KubaMiszcz/KwadraLampa/foto/2017-06-14 105718.jpg

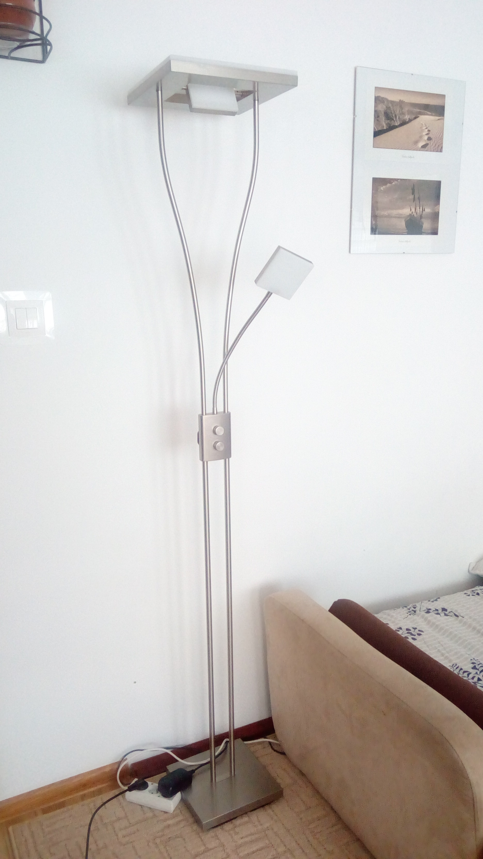
foto/2017-06-14 105718.jpg
