KubaMiszcz/KwadraLampa/foto/2017-06-14 105728.jpg

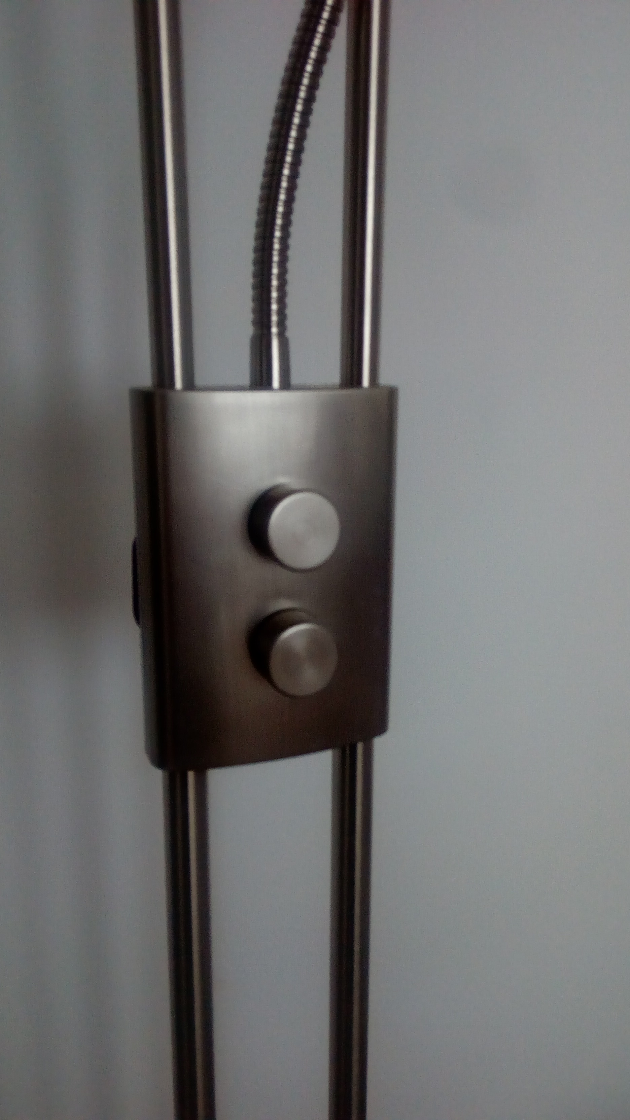
foto/2017-06-14 105728.jpg
