KubaMiszcz/KwadraLampa/foto/2017-06-14 105741.jpg

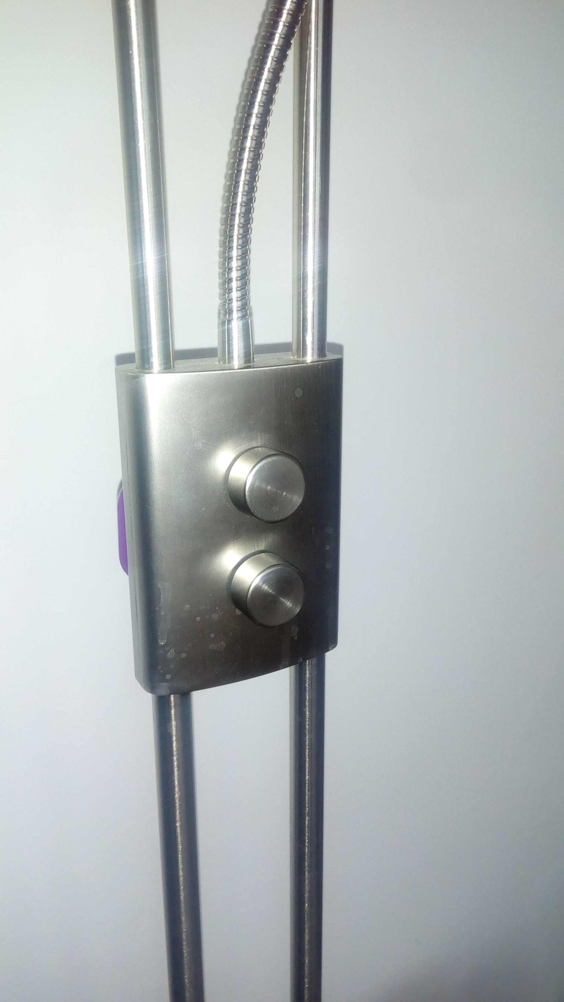
foto/2017-06-14 105741.jpg
