KubaMiszcz/KwadraLampa/foto/2017-06-16 212329.jpg

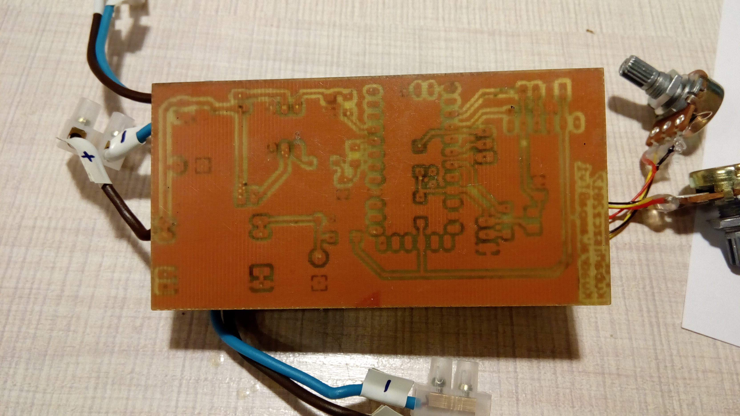
foto/2017-06-16 212329.jpg
