KubaMiszcz/KwadraLampa/foto/2017-06-16 212456.jpg

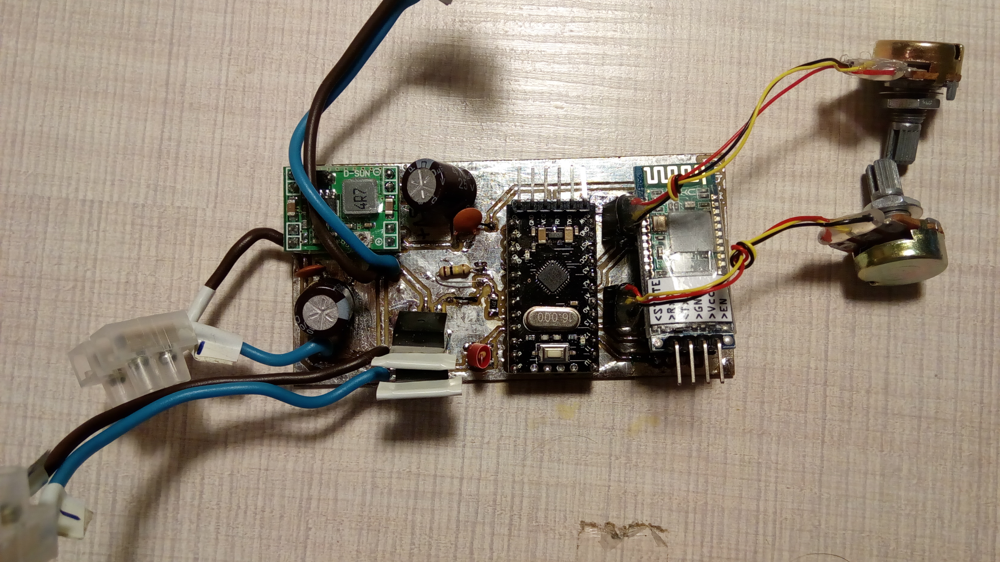
foto/2017-06-16 212456.jpg
