KubaMiszcz/KwadraLampa/foto/2017-06-16 212521.jpg

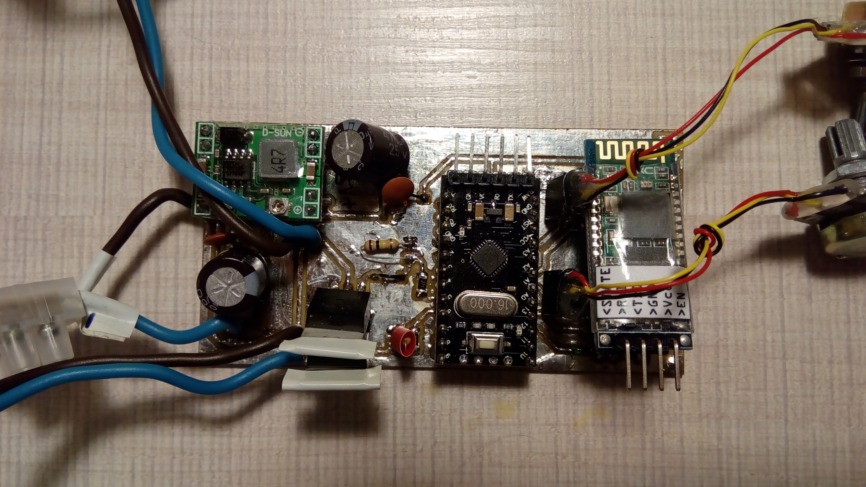
foto/2017-06-16 212521.jpg
