KubaMiszcz/KwadraLampa/foto/foto stara plytka oryginalna/2017-04-05 090402.jpg

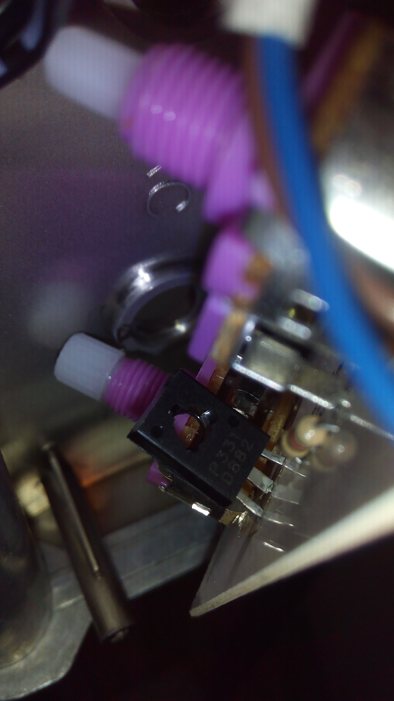
foto/foto stara plytka oryginalna/2017-04-05 090402.jpg
