KubaMiszcz/KwadraLampa/foto/foto stara plytka oryginalna/2017-04-05 090437.jpg

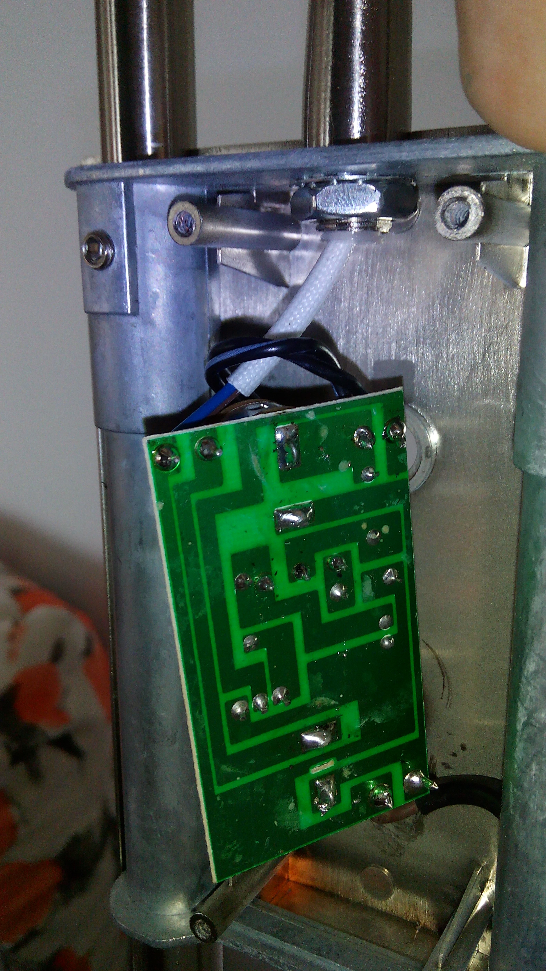
foto/foto stara plytka oryginalna/2017-04-05 090437.jpg
