KubaMiszcz/KwadraLampa/foto/foto stara plytka oryginalna/2017-04-20 123041.jpg

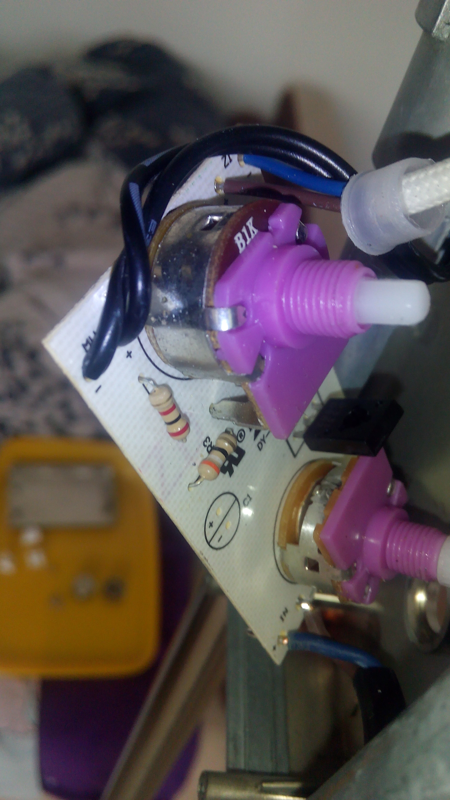
foto/foto stara plytka oryginalna/2017-04-20 123041.jpg
