KubaMiszcz/KwadraLampa/foto/foto stara plytka oryginalna/2017-04-20 140759.jpg

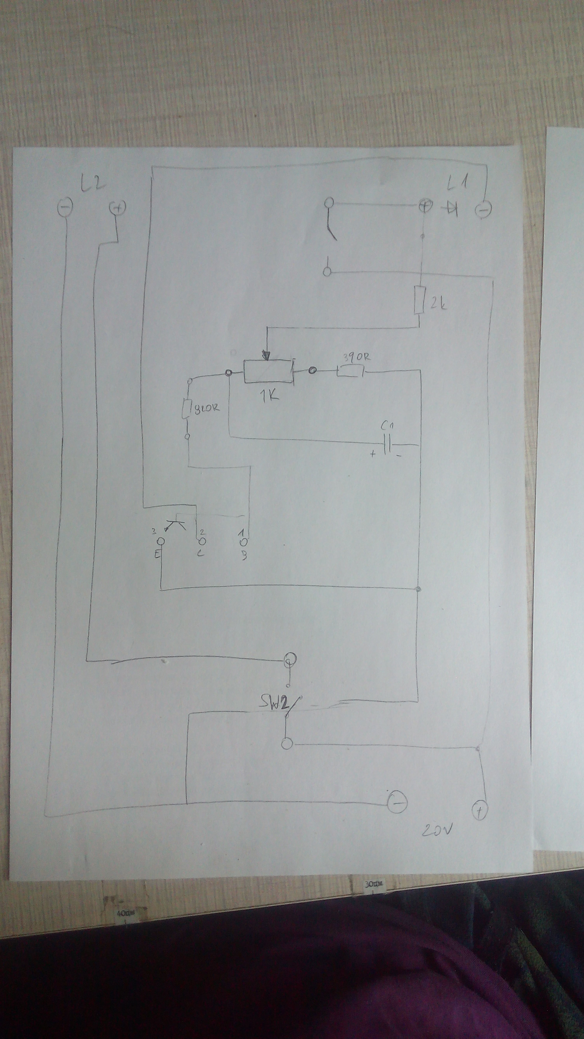
foto/foto stara plytka oryginalna/2017-04-20 140759.jpg
