KubaMiszcz/KwadraLampa/foto/foto stara plytka oryginalna/2017-04-21 072605.jpg

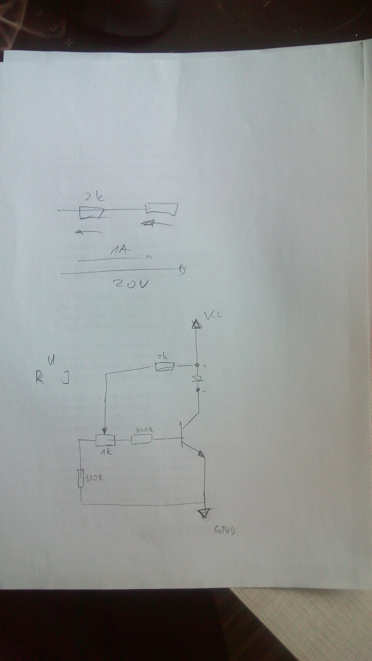
foto/foto stara plytka oryginalna/2017-04-21 072605.jpg
