KubaMiszcz/KwadraLampa/foto/Screenshot_20170625-214846-649.jpg

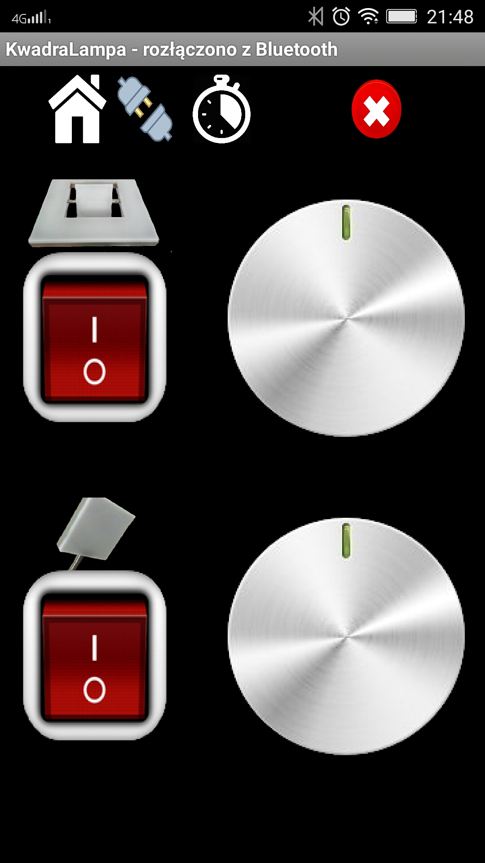
foto/Screenshot_20170625-214846-649.jpg
