KubaMiszcz/KwadraLampa/foto/Screenshot_20170625-214859-454.jpg

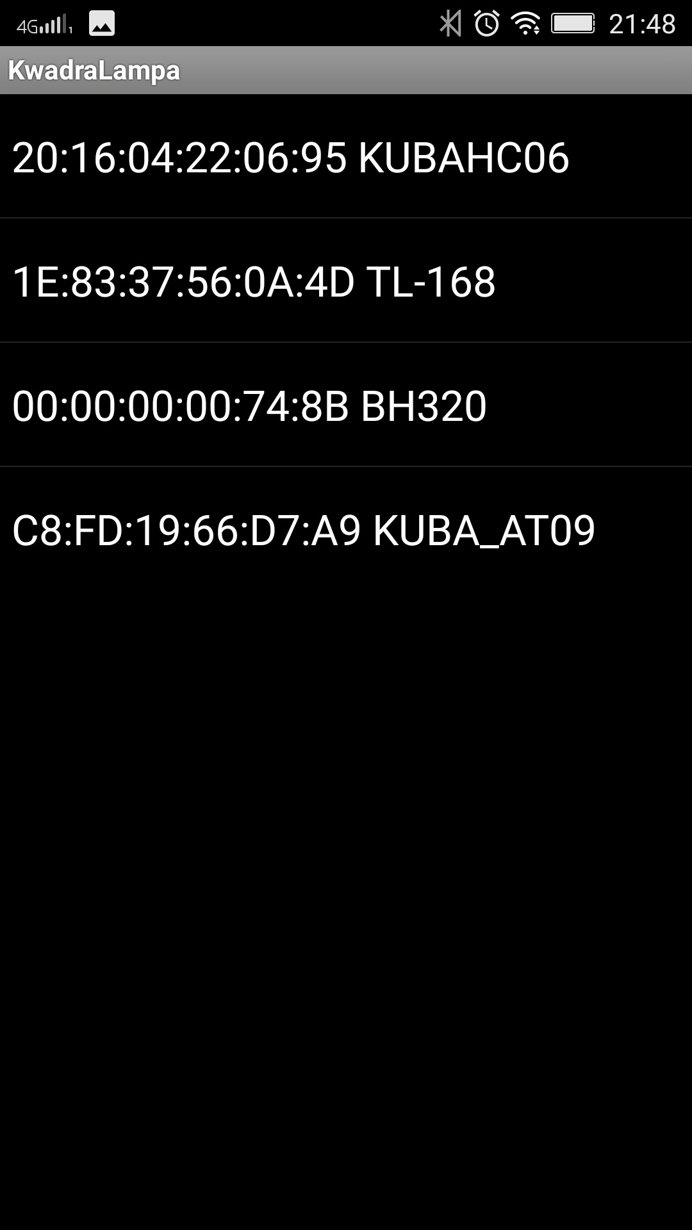
foto/Screenshot_20170625-214859-454.jpg
