KubaMiszcz/KwadraLampa/foto/Screenshot_20170625-214941-489.jpg

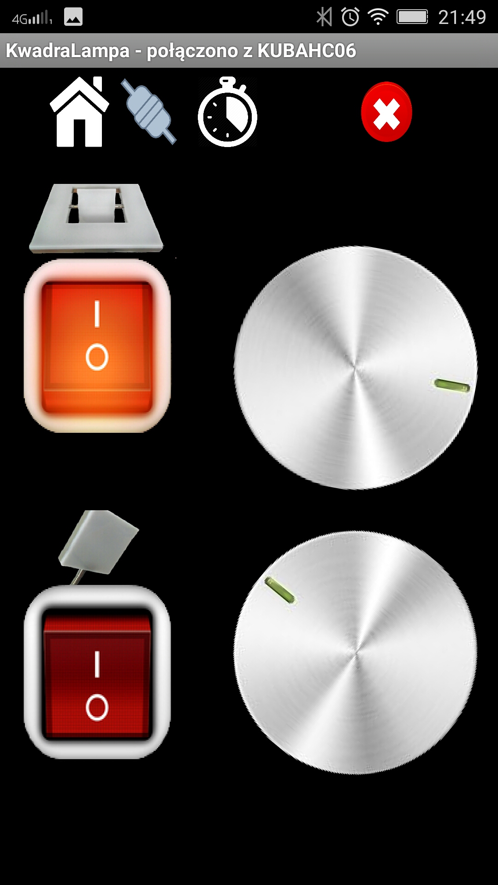
foto/Screenshot_20170625-214941-489.jpg
