KubaMiszcz/KwadraLampa/grafiki/=accepted/configmgtmv2.png

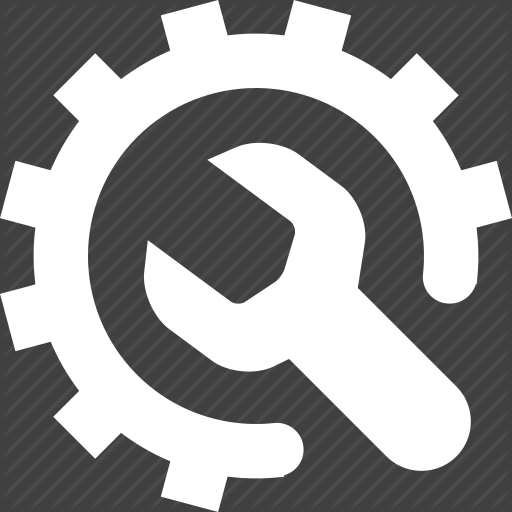
grafiki/=accepted/configmgtmv2.png
