KubaMiszcz/KwadraLampa/grafiki/=accepted/connected.png

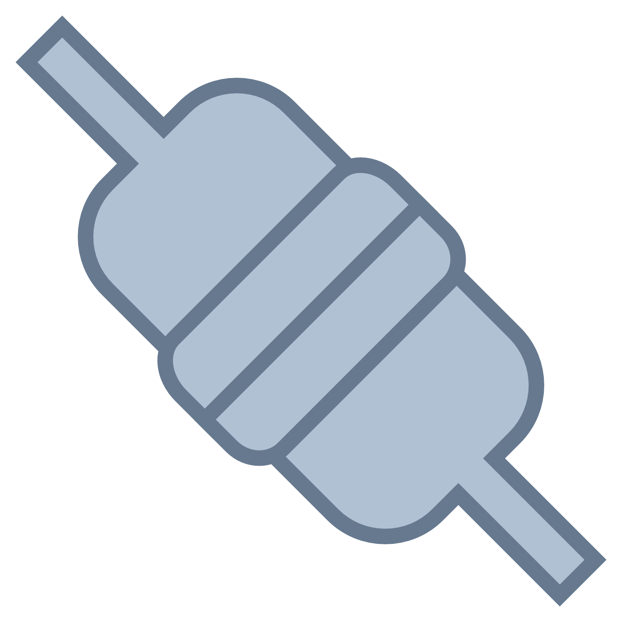
grafiki/=accepted/connected.png
