KubaMiszcz/KwadraLampa/grafiki/=accepted/disconnected.png

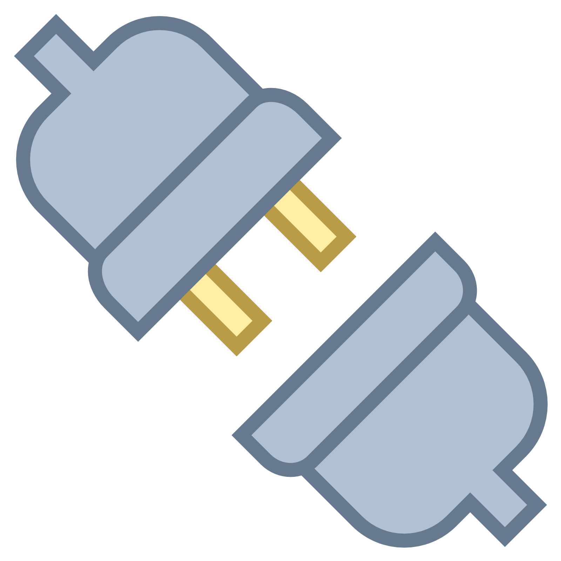
grafiki/=accepted/disconnected.png
