KubaMiszcz/KwadraLampa/grafiki/=accepted/rotaryframe.png

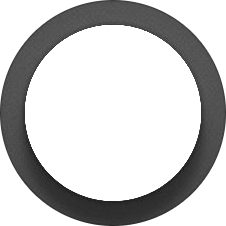
grafiki/=accepted/rotaryframe.png
