KubaMiszcz/KwadraLampa/grafiki/=accepted/rotaryknob.png

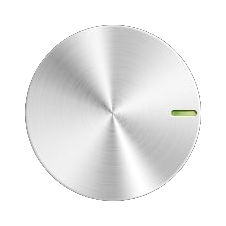
grafiki/=accepted/rotaryknob.png
