KubaMiszcz/KwadraLampa/grafiki/=accepted/rotaryknobv2.png

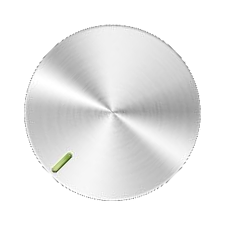
grafiki/=accepted/rotaryknobv2.png
