KubaMiszcz/KwadraLampa/grafiki/=accepted/rotaryknobv3.png

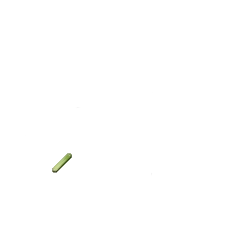
grafiki/=accepted/rotaryknobv3.png
