KubaMiszcz/KwadraLampa/grafiki/=accepted/tglOFF.png

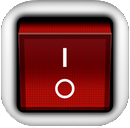
grafiki/=accepted/tglOFF.png
