KubaMiszcz/KwadraLampa/grafiki/=accepted/tglON.png

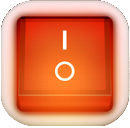
grafiki/=accepted/tglON.png
