KubaMiszcz/KwadraLampa/grafiki/rotary knob/1be09ef4f67cd16aef867e28d9eb9c2ec.jpg

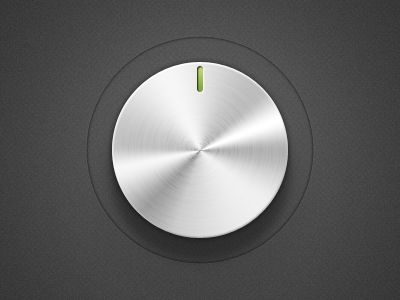
grafiki/rotary knob/1be09ef4f67cd16aef867e28d9eb9c2ec.jpg
