KubaMiszcz/KwadraLampa/grafiki/rotary knob/12.jpg

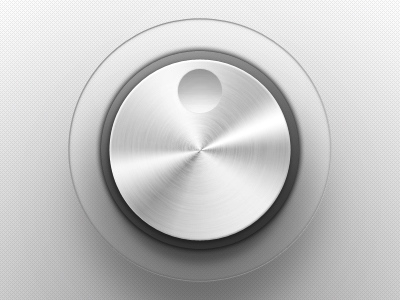
grafiki/rotary knob/12.jpg
