KubaMiszcz/KwadraLampa/grafiki/rotary knob/44b840771f93643ba0205818fd45a70e.jpg

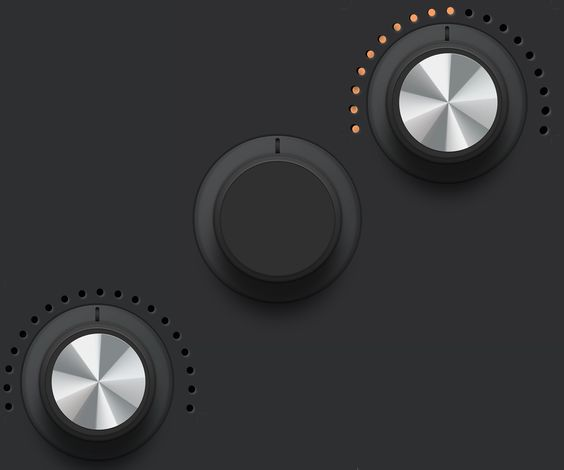
grafiki/rotary knob/44b840771f93643ba0205818fd45a70e.jpg
