KubaMiszcz/KwadraLampa/grafiki/rotary knob/175a313ea760b521a13a66fa4a31e26b.jpg

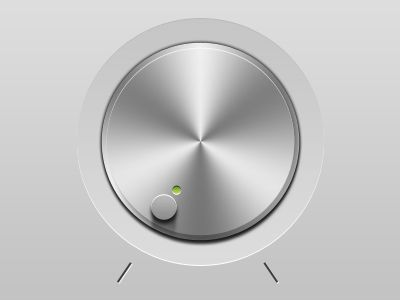
grafiki/rotary knob/175a313ea760b521a13a66fa4a31e26b.jpg
