KubaMiszcz/KwadraLampa/grafiki/rotary knob/0339cee554c793700000158fcb66db1.jpg

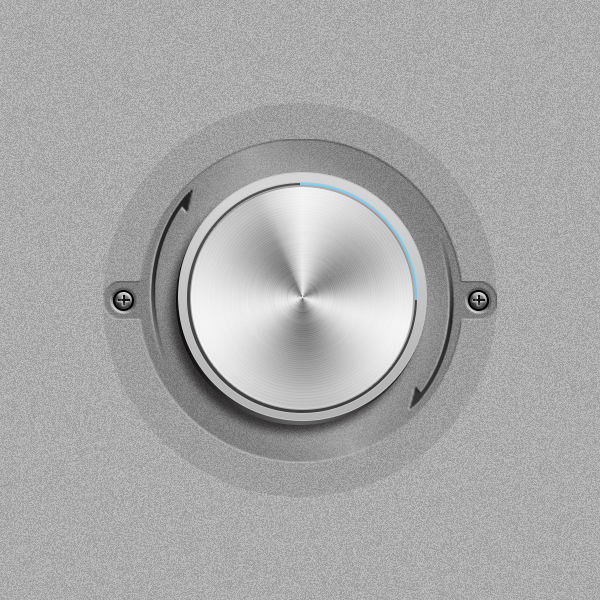
grafiki/rotary knob/0339cee554c793700000158fcb66db1.jpg
