KubaMiszcz/KwadraLampa/grafiki/rotary knob/658cad4266a4e6def83f9c6049b5e742.jpg

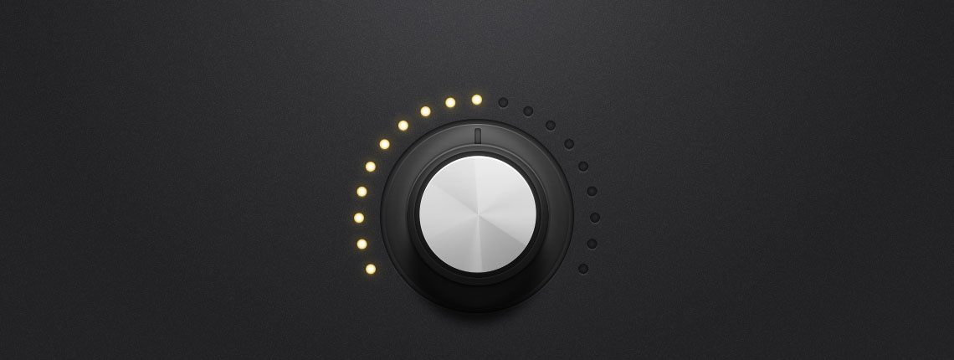
grafiki/rotary knob/658cad4266a4e6def83f9c6049b5e742.jpg
