KubaMiszcz/KwadraLampa/grafiki/rotary knob/201359c53ff9c94d0415b635d4622114.jpg

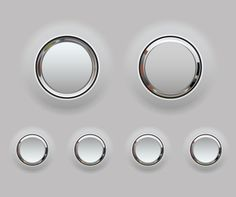
grafiki/rotary knob/201359c53ff9c94d0415b635d4622114.jpg
