KubaMiszcz/KwadraLampa/grafiki/rotary knob/13725800696028.jpg

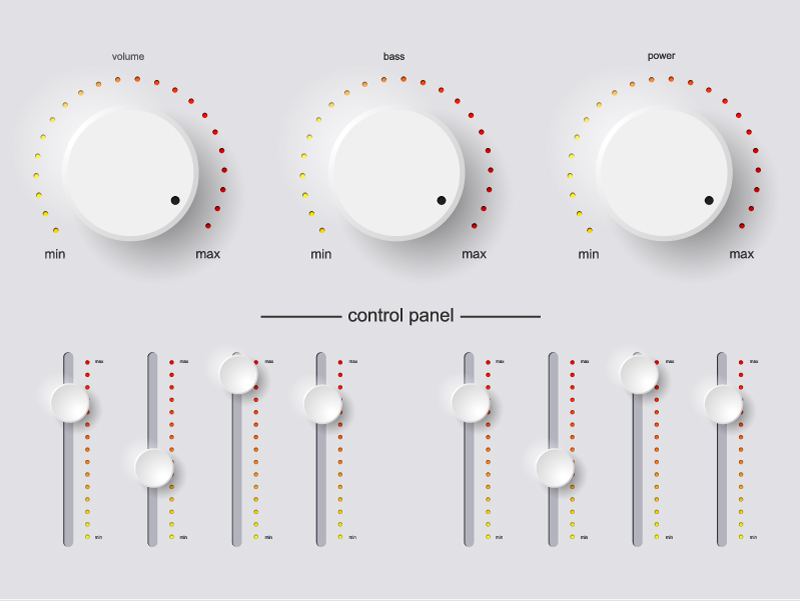
grafiki/rotary knob/13725800696028.jpg
