KubaMiszcz/KwadraLampa/grafiki/rotary knob/cc8fb4c5d4ede3740c84c0babd9590ac-d5dccy2.jpg

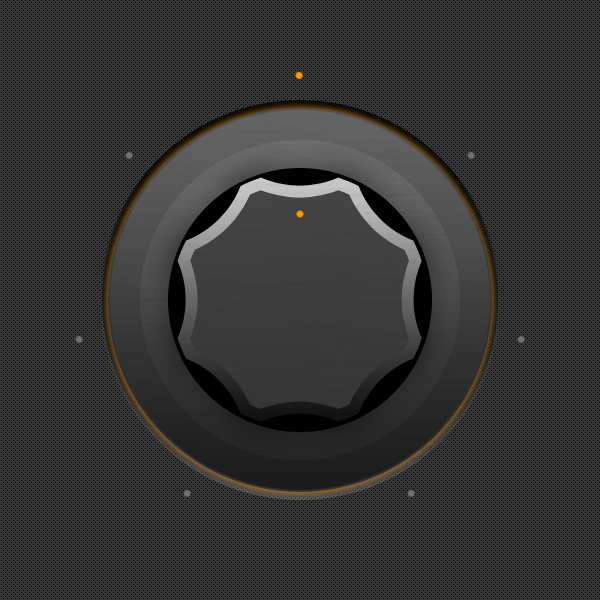
grafiki/rotary knob/cc8fb4c5d4ede3740c84c0babd9590ac-d5dccy2.jpg
