KubaMiszcz/KwadraLampa/grafiki/rotary knob/d845cab26f0945b9a81a3039507318fb.jpg

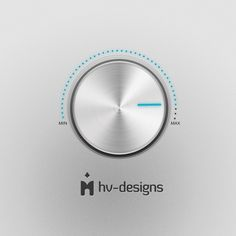
grafiki/rotary knob/d845cab26f0945b9a81a3039507318fb.jpg
