KubaMiszcz/KwadraLampa/grafiki/rotary knob/e2a8a074b16d124590965471c6b21355.jpg

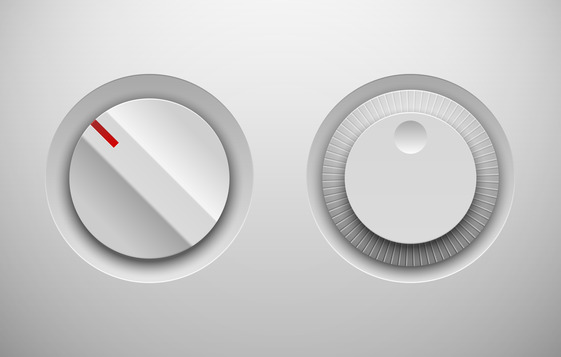
grafiki/rotary knob/e2a8a074b16d124590965471c6b21355.jpg
