KubaMiszcz/KwadraLampa/grafiki/rotary knob/elevator_btn_port.jpg

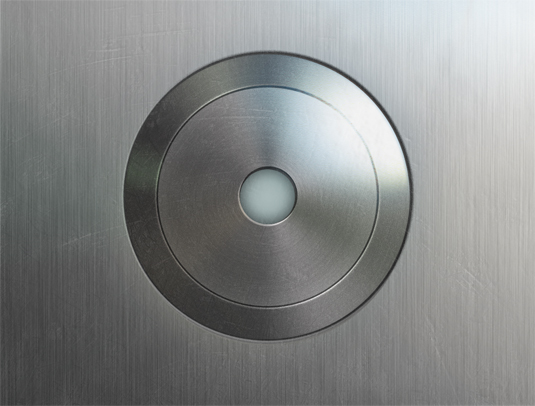
grafiki/rotary knob/elevator_btn_port.jpg
