KubaMiszcz/KwadraLampa/grafiki/rotary knob/High-quality-psd-files-1sept-34.jpg

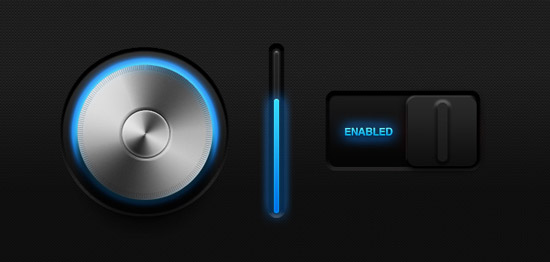
grafiki/rotary knob/High-quality-psd-files-1sept-34.jpg
