KubaMiszcz/KwadraLampa/grafiki/rotary knob/Knob-Style-Rotary-Switch-Plugin-with-jQuery-rotarySwitch.jpg

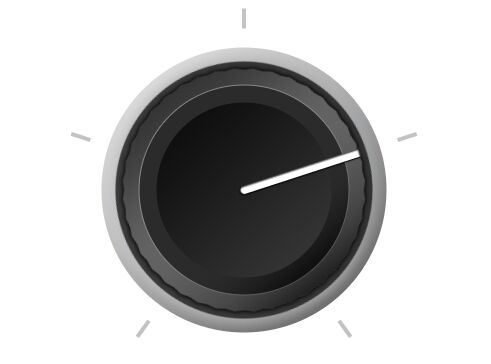
grafiki/rotary knob/Knob-Style-Rotary-Switch-Plugin-with-jQuery-rotarySwitch.jpg
