KubaMiszcz/KwadraLampa/grafiki/rotary knob/MzSwW.png

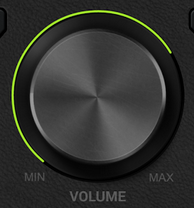
grafiki/rotary knob/MzSwW.png
