KubaMiszcz/KwadraLampa/grafiki/rotary knob/Nice-Touch-enabled-jQuery-Knob-Plugin-Knobby-js.jpg

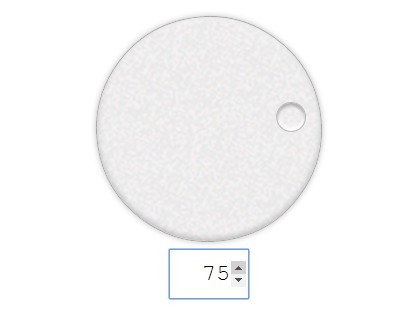
grafiki/rotary knob/Nice-Touch-enabled-jQuery-Knob-Plugin-Knobby-js.jpg
