KubaMiszcz/KwadraLampa/grafiki/rotary knob/P115491_PPT.jpg

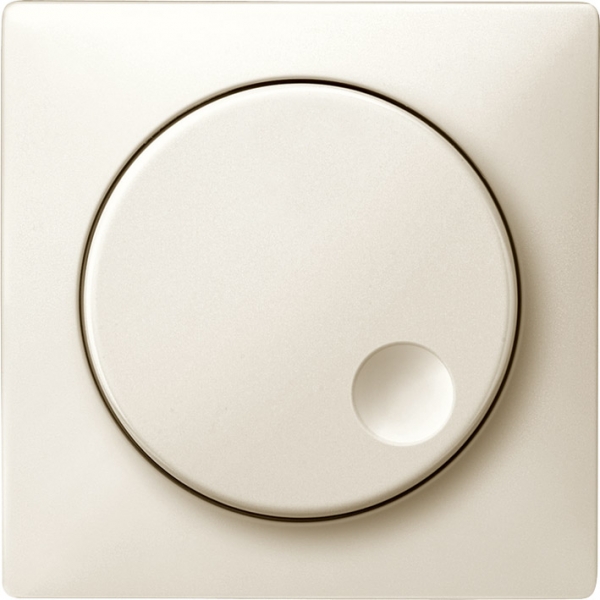
grafiki/rotary knob/P115491_PPT.jpg
