KubaMiszcz/KwadraLampa/grafiki/rotary knob/przycisk-audio-gui-interface-kit-gałka-knobz-suwak-przełącznika-ui-ui-kit_29-30000273.jpg

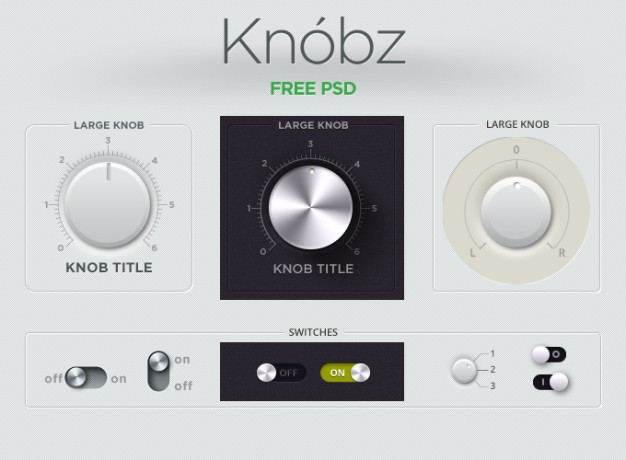
grafiki/rotary knob/przycisk-audio-gui-interface-kit-gałka-knobz-suwak-przełącznika-ui-ui-kit_29-30000273.jpg
