KubaMiszcz/KwadraLampa/grafiki/rotary knob/R2UWj.png

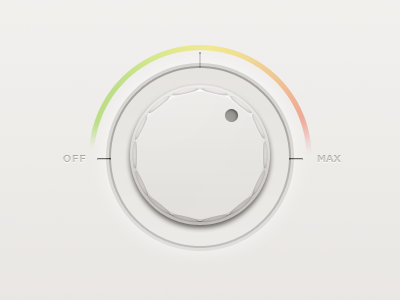
grafiki/rotary knob/R2UWj.png
