KubaMiszcz/KwadraLampa/grafiki/rotary knob/rotary_knob_android_custom_control-02.jpg

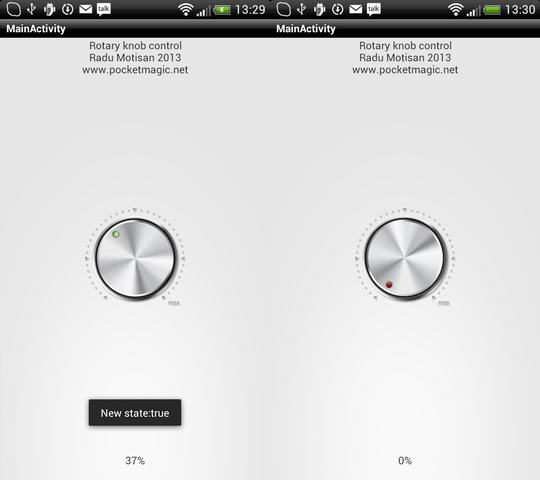
grafiki/rotary knob/rotary_knob_android_custom_control-02.jpg
