KubaMiszcz/KwadraLampa/grafiki/rotary knob/rotary_knob_android_custom_control.jpg

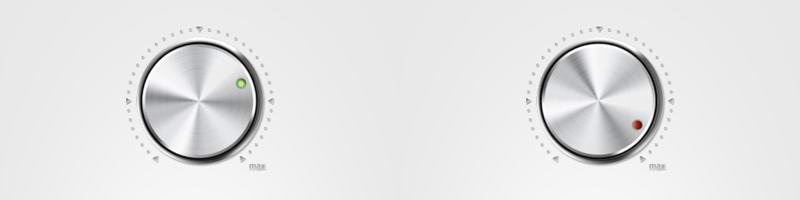
grafiki/rotary knob/rotary_knob_android_custom_control.jpg
