KubaMiszcz/KwadraLampa/grafiki/rotary knob/RTEmagicC_f594681baf.png.png

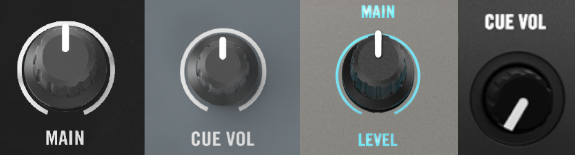
grafiki/rotary knob/RTEmagicC_f594681baf.png.png
