KubaMiszcz/KwadraLampa/grafiki/rotary knob/Screenshot_1.png

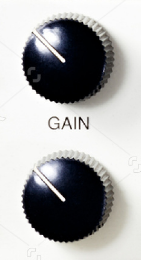
grafiki/rotary knob/Screenshot_1.png
