KubaMiszcz/KwadraLampa/grafiki/rotary knob/SK_small.png

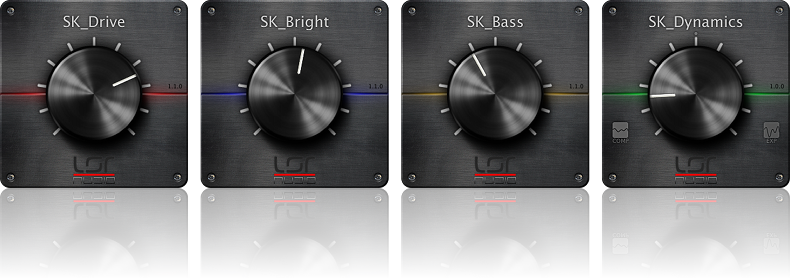
grafiki/rotary knob/SK_small.png
