KubaMiszcz/KwadraLampa/grafiki/rotary knob/volume-knobs-sw-s.jpg

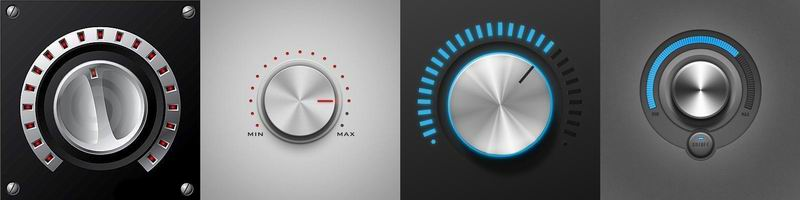
grafiki/rotary knob/volume-knobs-sw-s.jpg
