KubaMiszcz/KwadraLampa/grafiki/toggle btn/001-switch-on-off-light-dark-iphone-app-ui-elements-psd.jpg

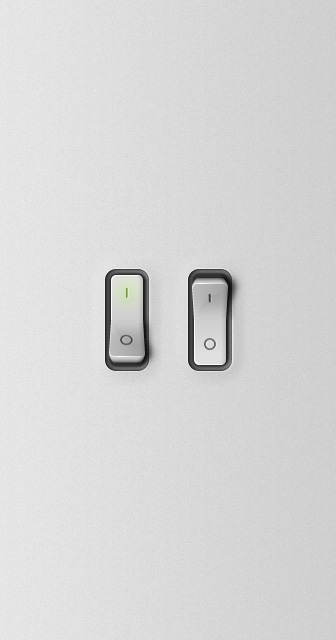
grafiki/toggle btn/001-switch-on-off-light-dark-iphone-app-ui-elements-psd.jpg
