KubaMiszcz/KwadraLampa/grafiki/toggle btn/0231ea23-d0f2-4197-880b-35ce445022ab.jpg

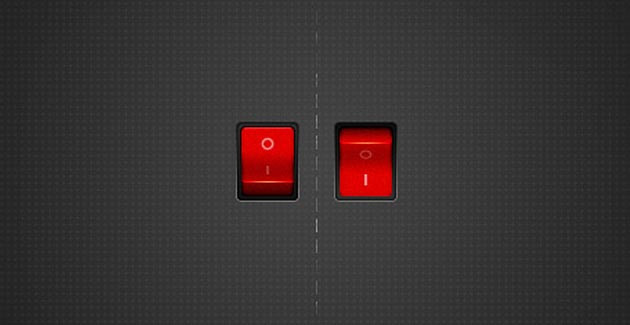
grafiki/toggle btn/0231ea23-d0f2-4197-880b-35ce445022ab.jpg
