KubaMiszcz/KwadraLampa/grafiki/toggle btn/Buttons-and-Switches-large-preview.jpg

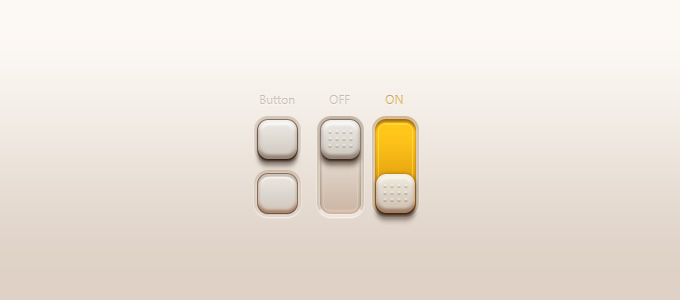
grafiki/toggle btn/Buttons-and-Switches-large-preview.jpg
