KubaMiszcz/KwadraLampa/grafiki/toggle btn/switch2_preview.png

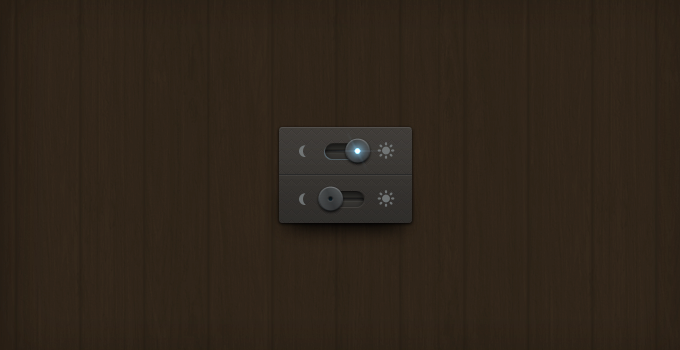
grafiki/toggle btn/switch2_preview.png
