KubaMiszcz/KwadraLampa/grafiki/toggle btn/switch-toggle-psd-02.jpg

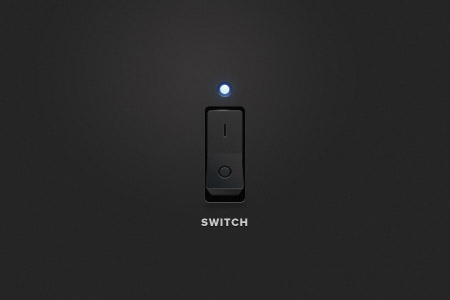
grafiki/toggle btn/switch-toggle-psd-02.jpg
