KubaMiszcz/KwadraLampa/grafiki/toggle btn/switch-toggle-psd-04.jpg

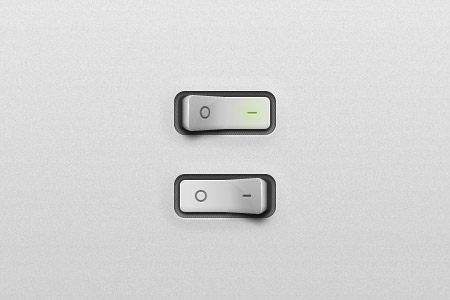
grafiki/toggle btn/switch-toggle-psd-04.jpg
