KubaMiszcz/KwadraLampa/plytka Eagle v2 90st/!PCB!bottomLayer.png

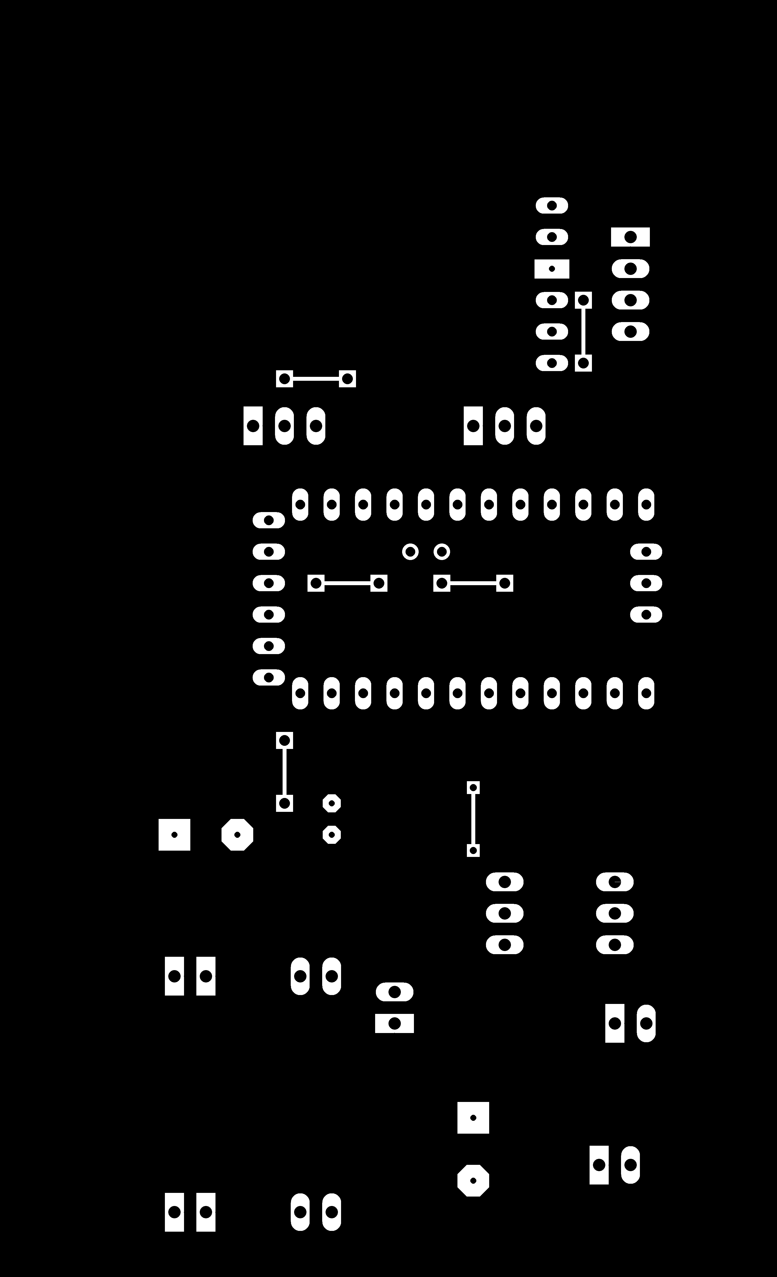
plytka Eagle v2 90st/!PCB!bottomLayer.png
