KubaMiszcz/KwadraLampa/plytka Eagle v2 90st/!PCB!DescriptionLayer.png

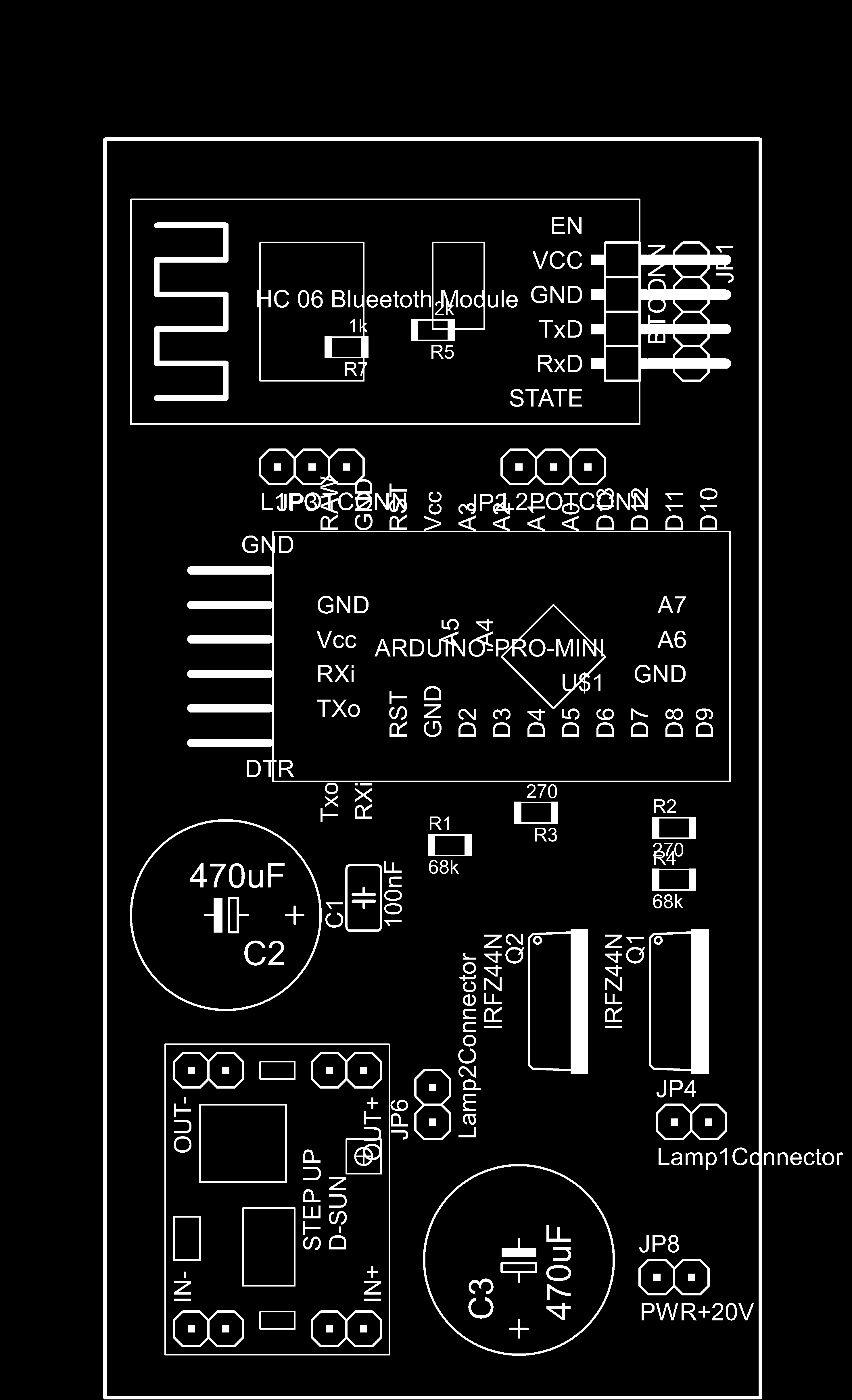
plytka Eagle v2 90st/!PCB!DescriptionLayer.png
