KubaMiszcz/KwadraLampa/plytka Eagle v2 90st/!PCB!TopLayer.png

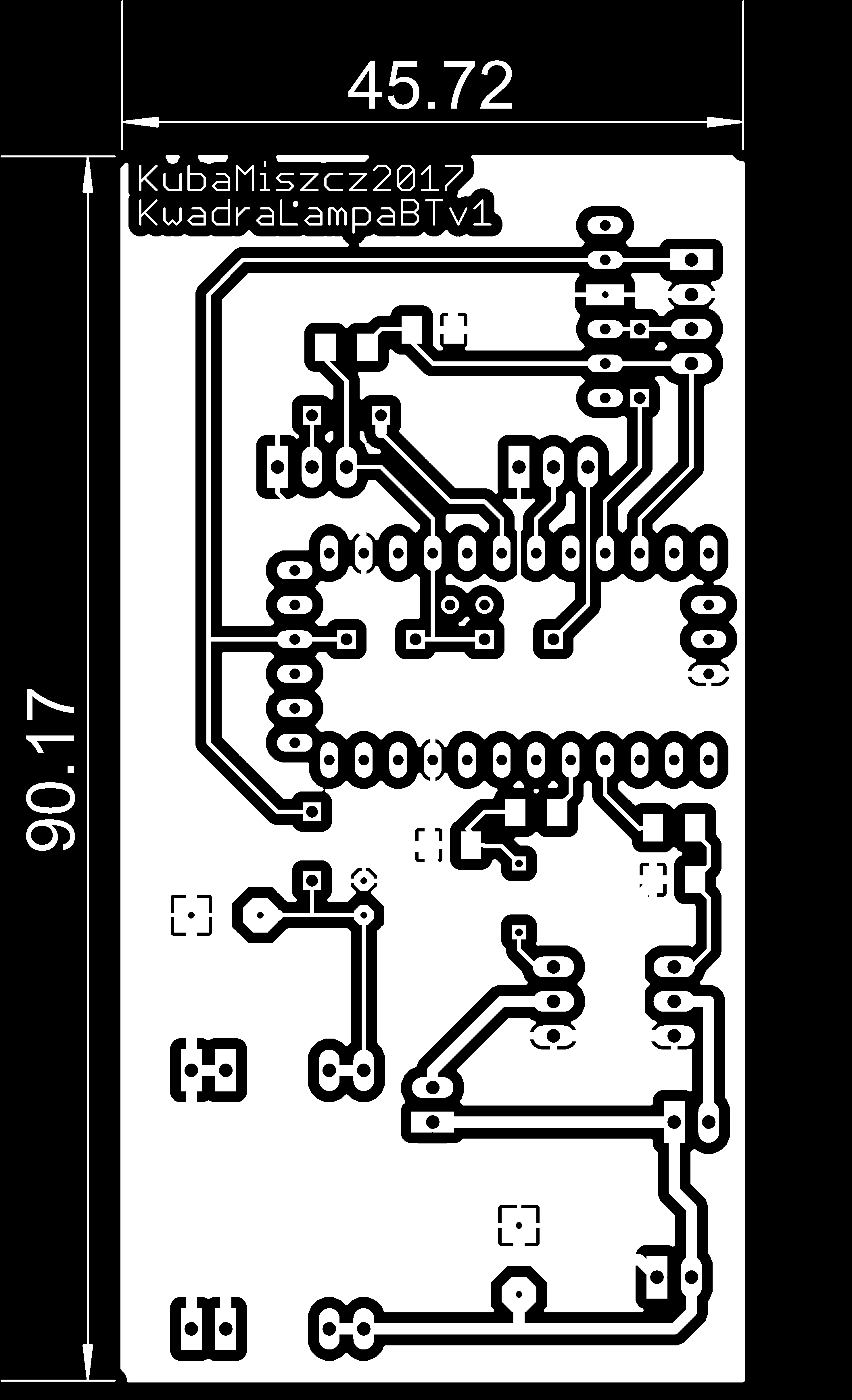
plytka Eagle v2 90st/!PCB!TopLayer.png
