KubaMiszcz/KwadraLampa/plytka Eagle v2 90st/Clipboard.png

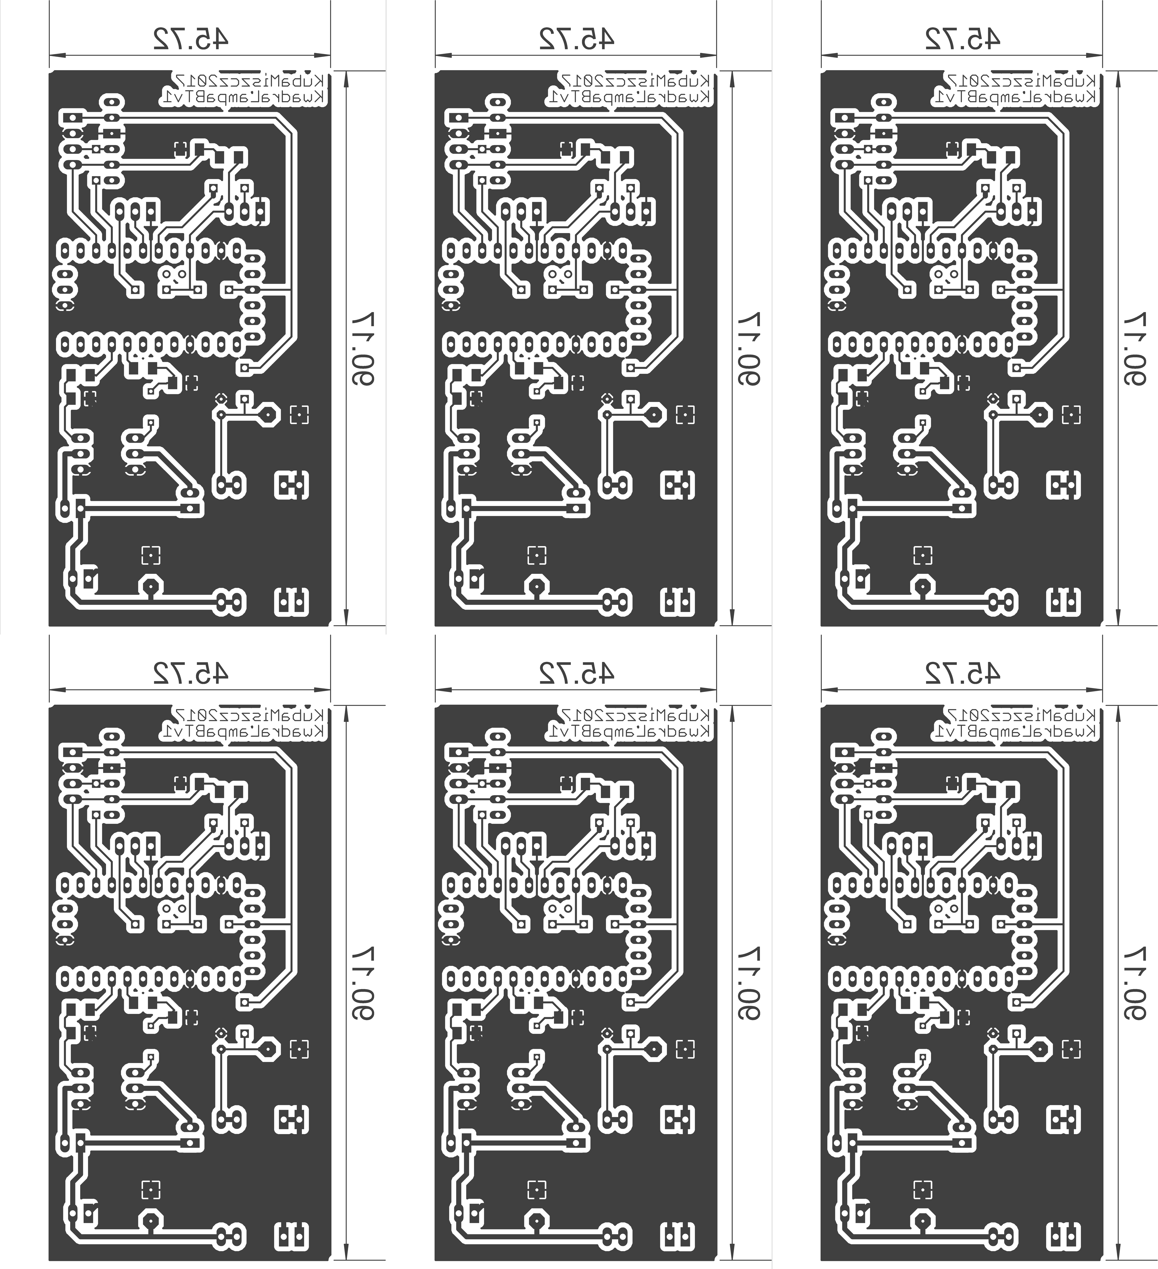
plytka Eagle v2 90st/Clipboard.png
