KubaMiszcz/KwadraLampa/LampaStojacaDriverBT/LampaStojacaDriverBT/SharedObjects.cpp

// 
// 
// 

#include "SharedObjects.h"
Time SharedObjectsClass::currentTime = { 0,0,0 };
String SharedObjectsClass::MessageToSend = "";


void SharedObjectsClass::init()
{

}


SharedObjectsClass SharedObjects;
